kihunsong22/Air-quality-monitoring-system/Pictures/V1_Server.png

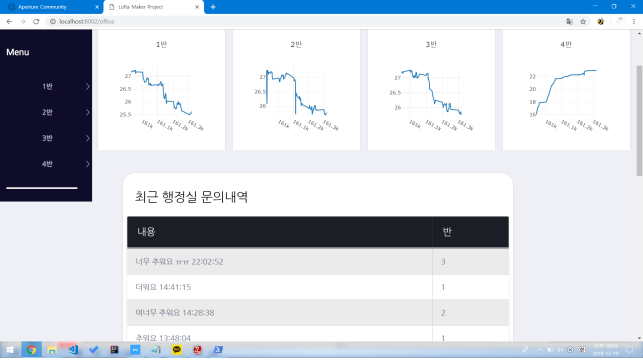
Pictures/V1_Server.png
