kihunsong22/Air-quality-monitoring-system/V2/Pictures/PCB/PCB (1).jpg

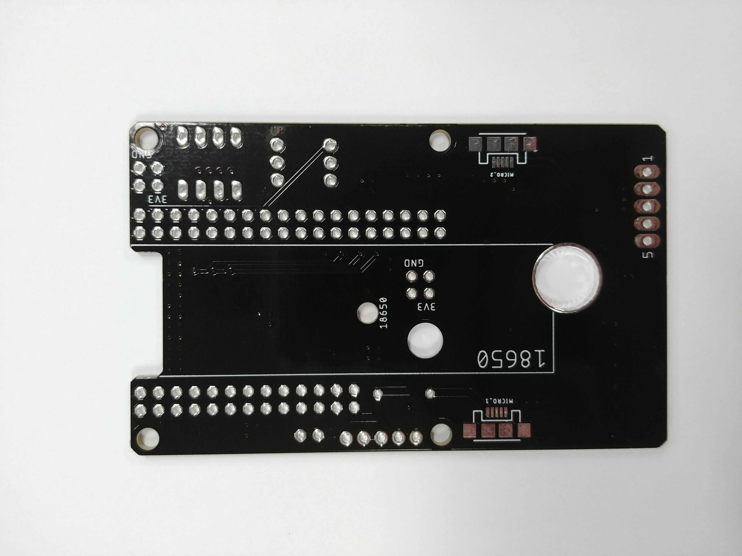
V2/Pictures/PCB/PCB (1).jpg
