kihunsong22/Air-quality-monitoring-system/V2/Pictures/PCB/PCB.jpg

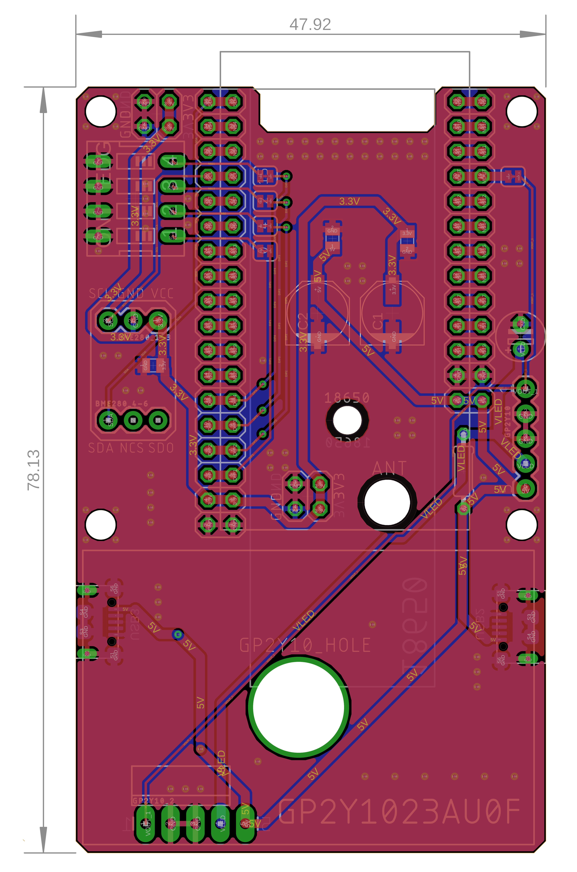
V2/Pictures/PCB/PCB.jpg
