kihunsong22/Air-quality-monitoring-system/V2/Pictures/Sensor Nodes/IMG_0242.jpg

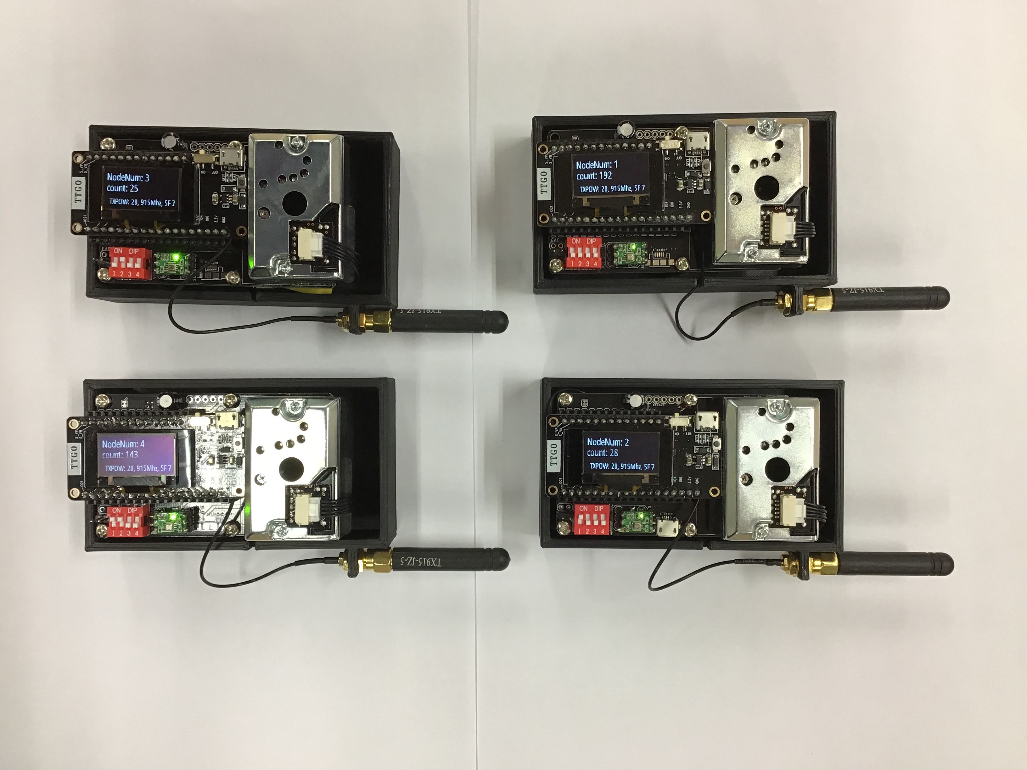
V2/Pictures/Sensor Nodes/IMG_0242.jpg
