kihunsong22/Air-quality-monitoring-system/V2/Pictures/Sensor Nodes/IMG_0246.jpg

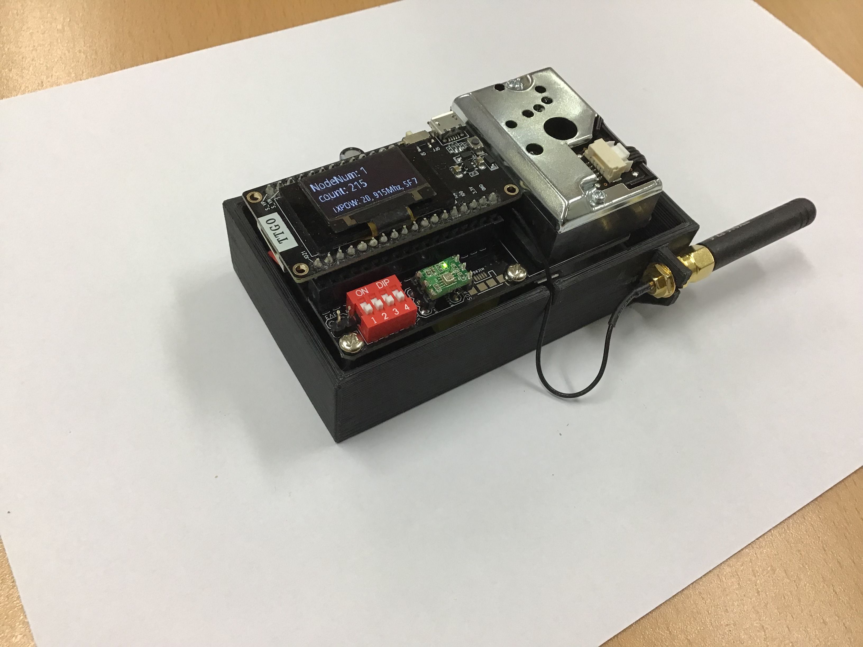
V2/Pictures/Sensor Nodes/IMG_0246.jpg
