kihunsong22/Air-quality-monitoring-system/V2/Pictures/Server/classroom.jpg

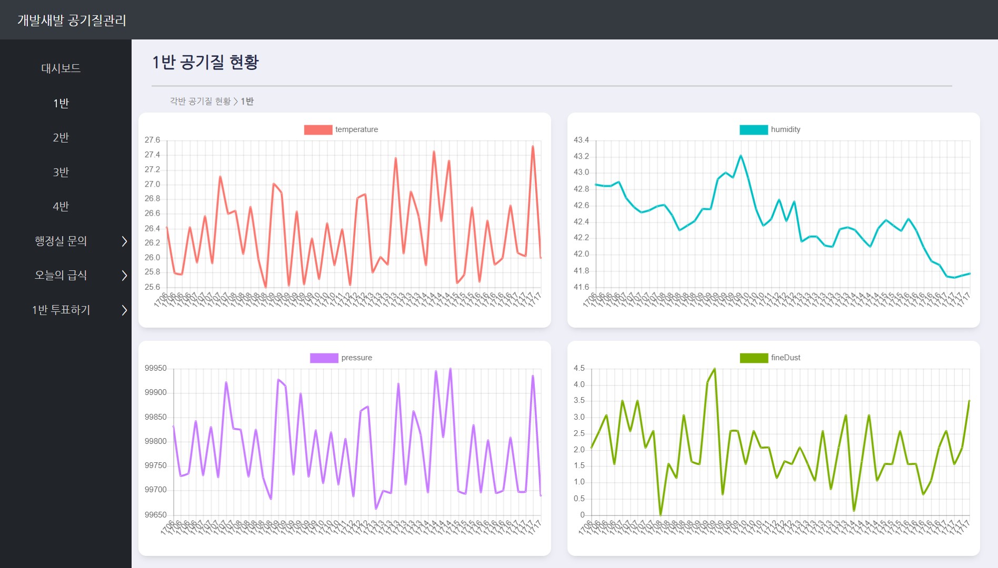
V2/Pictures/Server/classroom.jpg
